synfinatic/delaytimer/ltspice/delaytimer.asc

C1: cap; .1µf
C2: polcap; 100µf
C4: cap; .1µf
D1: diode; 1N4148
M1: nmos; IRLML6344
Q1: pnp; 2N3906
Q2: pnp; 2N3906
Q3: npn; 2N3904
Q4: npn; 2N3904
R1: res; 100k
R2: res; 47k
R3: res; 2.2k
R4: res; 10k
R5: res; 10k
R6: res; 2.2k
R7: res; 2.2k
R9: res; 2.2k
R10: res; 10k
R12: res; 1k
S1: sw; Switch1
U1: NE555
V1: voltage; 12V
V2: voltage; PULSE(0 5 5 .0001 .0001 20)
Named nets: 0, THRS, Output, VCC, 12V, Sw1Ctrl, SwOut, TCtrl, Trig, VccCtrl, load
.model Switch1 SW(Ron=1 Roff=100Meg Vt=.5 Vh=-.4)
.tran 60sec startup
Based on the design by Rob Paisley
http://home.cogeco.ca/~rpaisley4/LM555.html#30
Current specs provide a 5sec delay using 100uF/47k cap/res
120 = 100ma Load @ 12V
10 = ~1A Load @ 12V
